Skyler-Cornell/E90-Embedded-Audio-Effects-Platform/Firmware/Audio_Processor_E90/Core/Inc/CONSTANTS.h

/*
 * CONSTANTS.h
 *
 *  Created on: Jan 22, 2021
 *      Author: skylercornell
 */

#ifndef INC_CONSTANTS_H_
#define INC_CONSTANTS_H_



#endif /* INC_CONSTANTS_H_ */

#include "main.h"


// DSP CONSTANTS
#define SAMPLE_RATE 48000 	 // Nominal sample rate
#define SAMPLE_RATE_ACTUAL 46875 //actual sample rate
#define BIT_DEPTH 24




#define PI (float)3.14159265359
